aliaafee/Tennis/src/charMap.h

#pragma once
// шрифты для вывода текста
const uint8_t _charMap[][5] PROGMEM = {
    {0x00, 0x00, 0x00, 0x00, 0x00}, //   0x20 32
    {0x00, 0x00, 0x6f, 0x00, 0x00}, // ! 0x21 33
    {0x00, 0x07, 0x00, 0x07, 0x00}, // " 0x22 34
    {0x14, 0x7f, 0x14, 0x7f, 0x14}, // # 0x23 35
    {0x8C, 0x92, 0xFF, 0x92, 0x62}, // $ 0x24 36
    {0x23, 0x13, 0x08, 0x64, 0x62}, // % 0x25 37
    {0x36, 0x49, 0x56, 0x20, 0x50}, // & 0x26 38
    {0x00, 0x00, 0x07, 0x00, 0x00}, // ' 0x27 39
    {0x00, 0x1c, 0x22, 0x41, 0x00}, // ( 0x28 40
    {0x00, 0x41, 0x22, 0x1c, 0x00}, // ) 0x29 41
    {0x14, 0x08, 0x3e, 0x08, 0x14}, // * 0x2a 42
    {0x08, 0x08, 0x3e, 0x08, 0x08}, // + 0x2b 43
    {0x00, 0x50, 0x30, 0x00, 0x00}, // , 0x2c 44
    {0x08, 0x08, 0x08, 0x08, 0x08}, // - 0x2d 45
    {0x00, 0x60, 0x60, 0x00, 0x00}, // . 0x2e 46
    {0x20, 0x10, 0x08, 0x04, 0x02}, // / 0x2f 47
    {0x3e, 0x51, 0x49, 0x45, 0x3e}, // 0 0x30 48
    {0x00, 0x42, 0x7f, 0x40, 0x00}, // 1 0x31 49
    {0x42, 0x61, 0x51, 0x49, 0x46}, // 2 0x32 50
    {0x21, 0x41, 0x45, 0x4b, 0x31}, // 3 0x33 51
    {0x18, 0x14, 0x12, 0x7f, 0x10}, // 4 0x34 52
    {0x27, 0x45, 0x45, 0x45, 0x39}, // 5 0x35 53
    {0x3c, 0x4a, 0x49, 0x49, 0x30}, // 6 0x36 54
    {0x01, 0x71, 0x09, 0x05, 0x03}, // 7 0x37 55
    {0x36, 0x49, 0x49, 0x49, 0x36}, // 8 0x38 56
    {0x06, 0x49, 0x49, 0x29, 0x1e}, // 9 0x39 57
    {0x00, 0x36, 0x36, 0x00, 0x00}, // : 0x3a 58
    {0x00, 0x56, 0x36, 0x00, 0x00}, // ; 0x3b 59
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
    {0x7c, 0x40, 0x7c, 0x40, 0xfc}, //щ
    {0x04, 0x7c, 0x50, 0x50, 0x20}, //ъ
    {0x7c, 0x50, 0x50, 0x20, 0x7c}, //ы
    {0x7c, 0x50, 0x50, 0x20, 0x00}, //ь
    {0x28, 0x44, 0x54, 0x54, 0x38}, //э
    {0x7c, 0x10, 0x38, 0x44, 0x38}, //ю
    {0x08, 0x54, 0x34, 0x14, 0x7c}, //я 255
*/
};
